johnlamb/LambBT/ergogen/output/outlines/cutout_circle_small_inner_wall.dxf

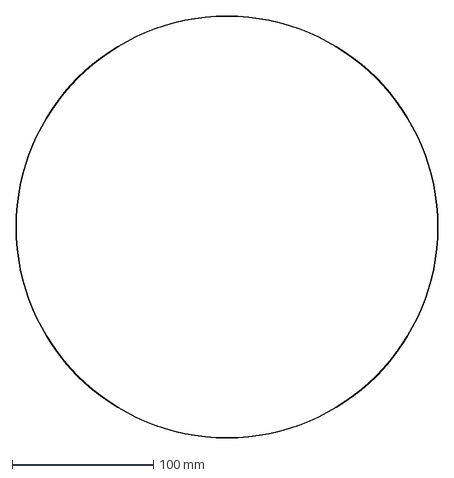
[picture p19: CAD file, 2023-08-09]
ergogen/output/outlines/cutout_circle_small_inner_wall.dxf
299.0 x 299.0 mm
