johnlamb/LambBT/ergogen/output/outlines/standoff.dxf

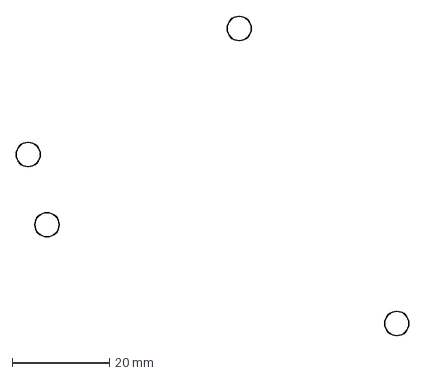
[picture p20: CAD file, 2023-08-09]
ergogen/output/outlines/standoff.dxf
81.0 x 65.8 mm
