johnlamb/LambBT/ergogen/output/outlines/pcb.dxf

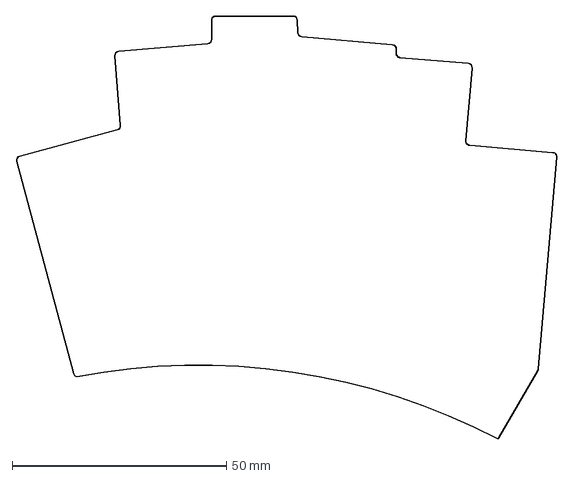
[picture p21: CAD file, 2023-08-09]
ergogen/output/outlines/pcb.dxf
126.2 x 98.7 mm
