johnlamb/LambBT/ergogen/output/outlines/switches.dxf

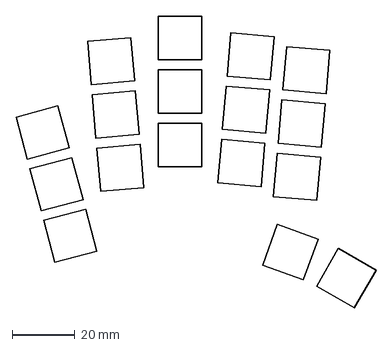
[picture p22: CAD file, 2023-08-09]
ergogen/output/outlines/switches.dxf
114.3 x 92.6 mm
